siddacious/SA-45/images/fuuuuuuuuuck.png

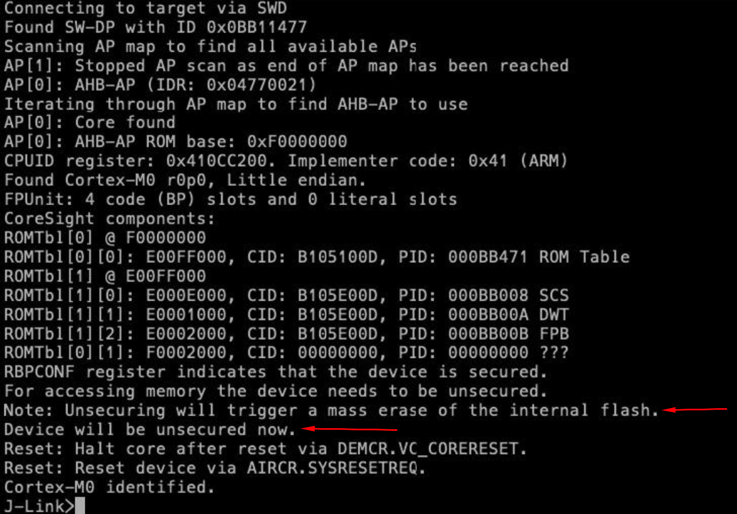
images/fuuuuuuuuuck.png
