siddacious/SA-45/images/guess_ill_stick_to_my_day_job.png

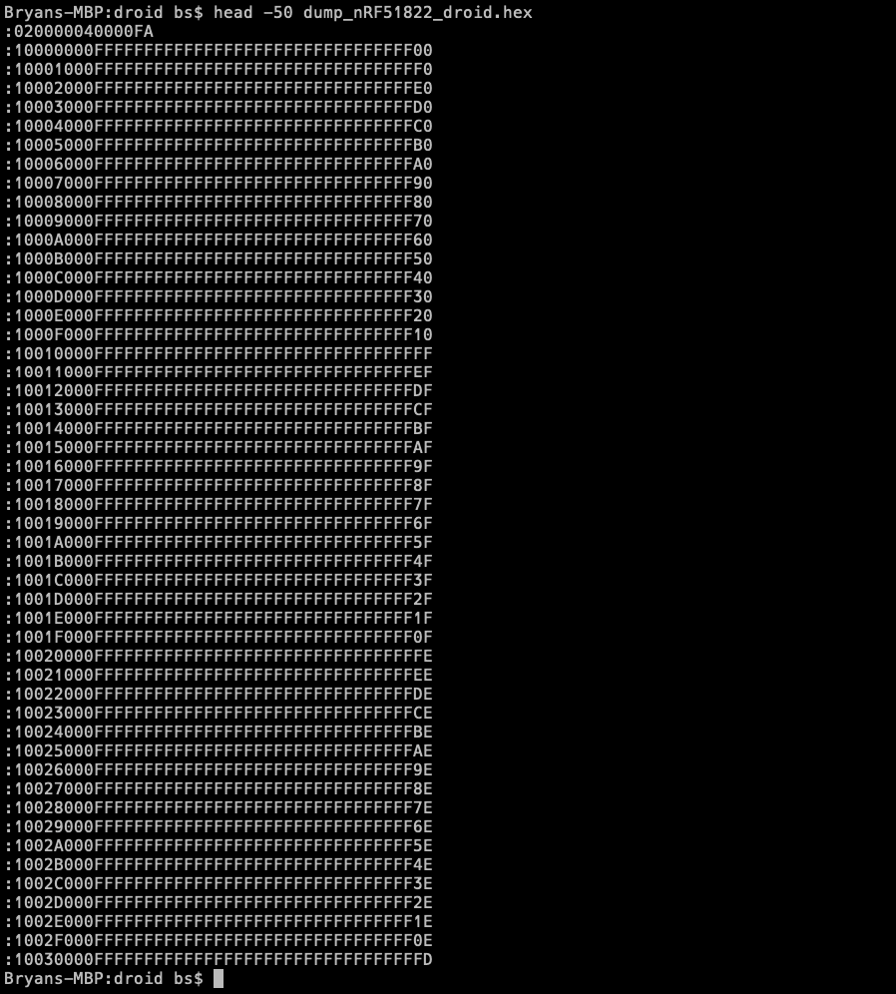
images/guess_ill_stick_to_my_day_job.png
