siddacious/SA-45/images/S20190909_001.jpg

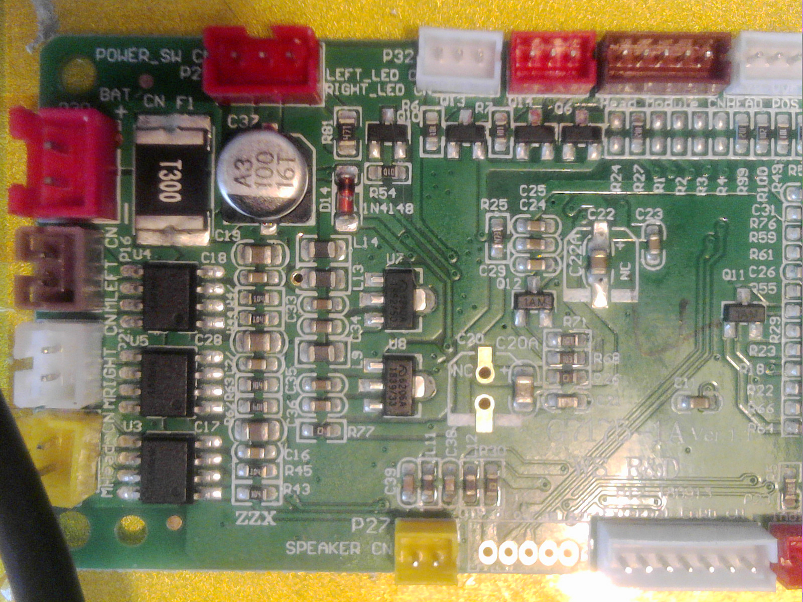
images/S20190909_001.jpg
