siddacious/SA-45/images/S20190909_002.jpg

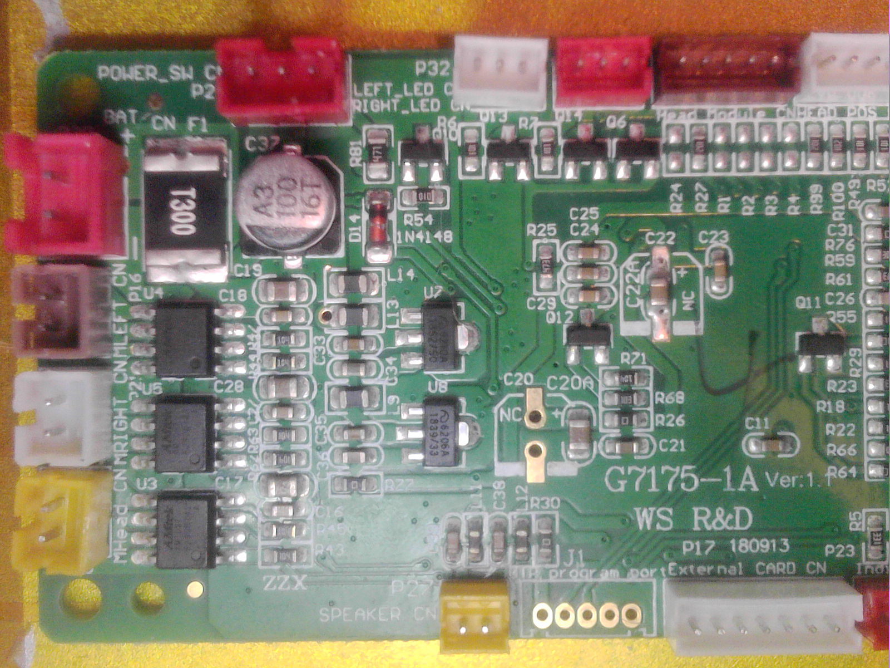
images/S20190909_002.jpg
