siddacious/SA-45/images/S20190909_003.jpg

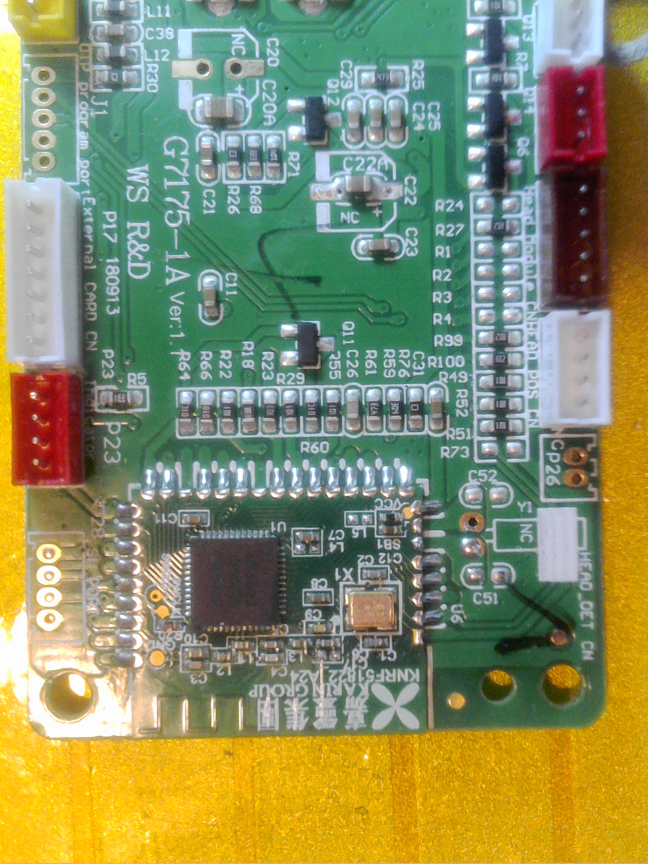
images/S20190909_003.jpg
