siddacious/SA-45/images/S20190909_006.jpg

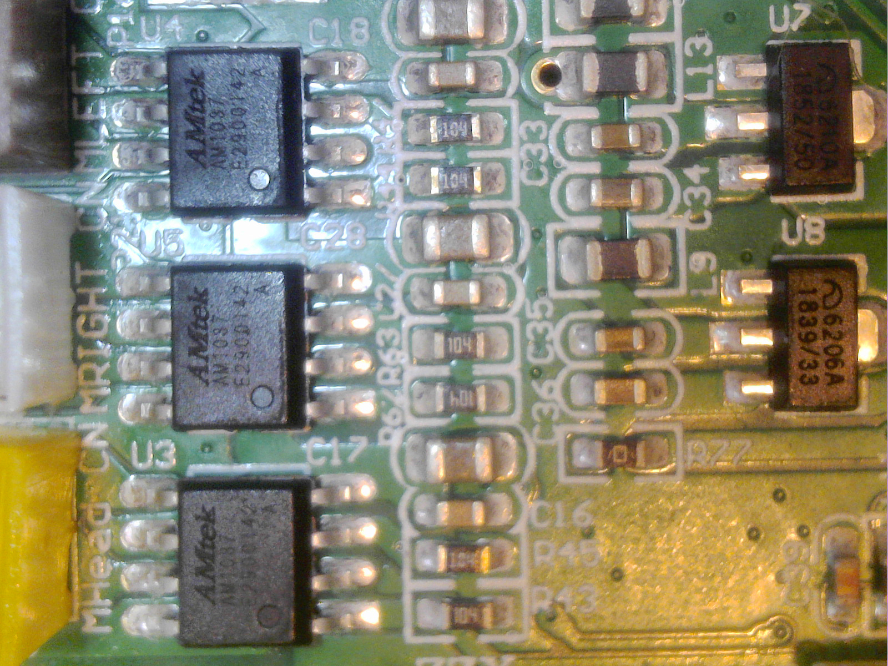
images/S20190909_006.jpg
