siddacious/SA-45/images/S20190909_007.jpg

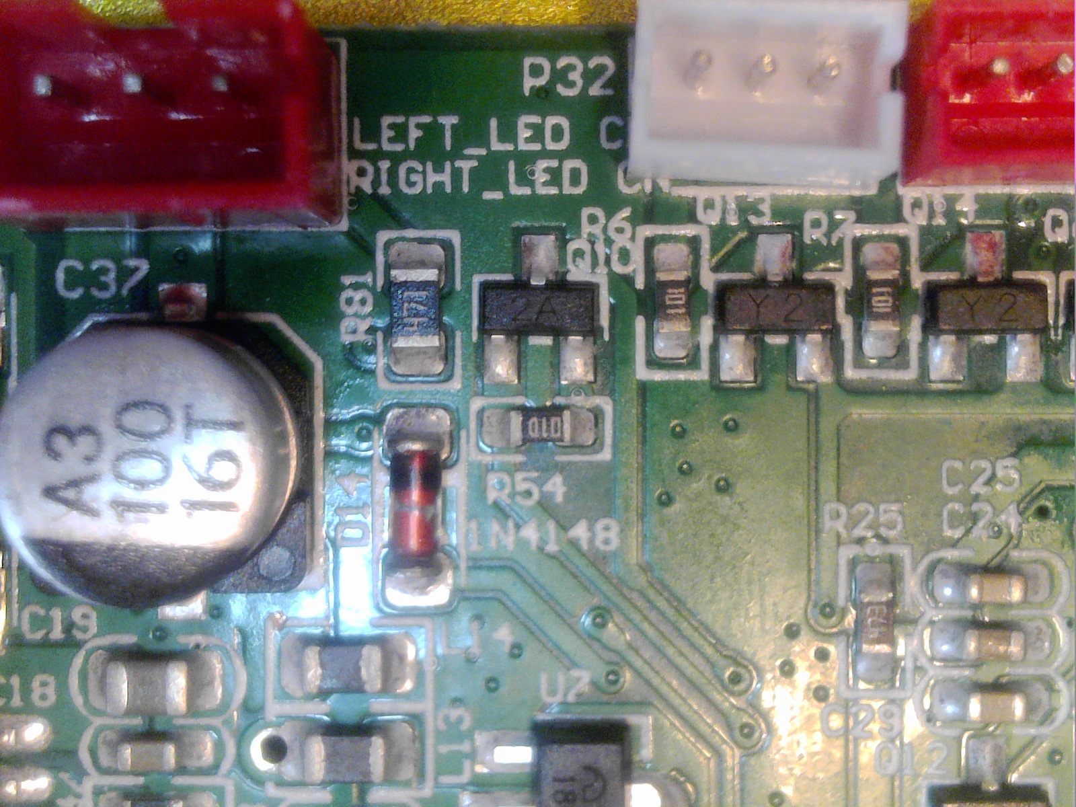
images/S20190909_007.jpg
