siddacious/SA-45/images/S20190909_009.jpg

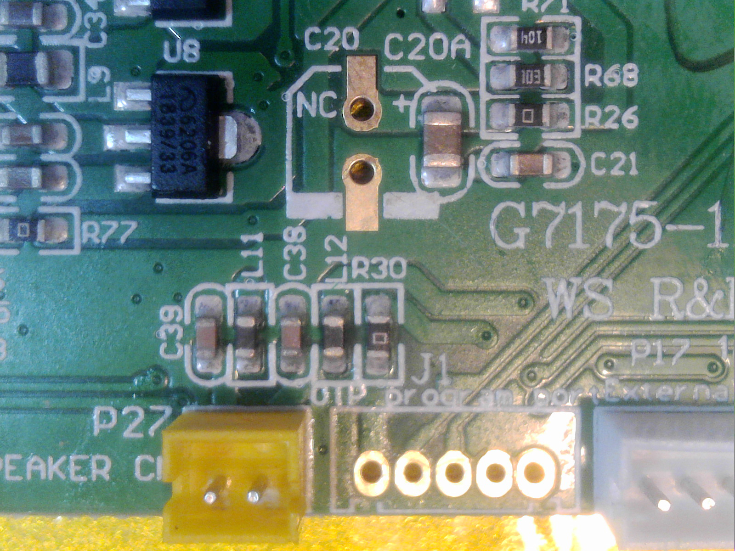
images/S20190909_009.jpg
