siddacious/SA-45/images/S20190909_010.jpg

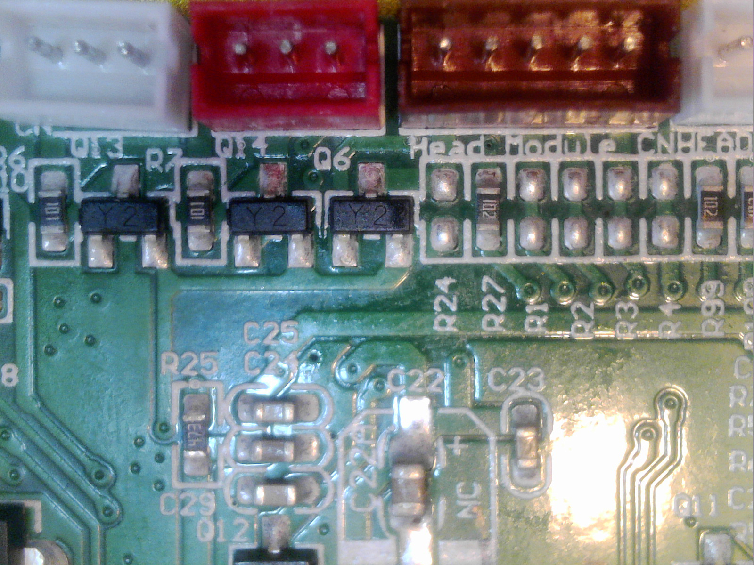
images/S20190909_010.jpg
