siddacious/SA-45/images/S20190909_011.jpg

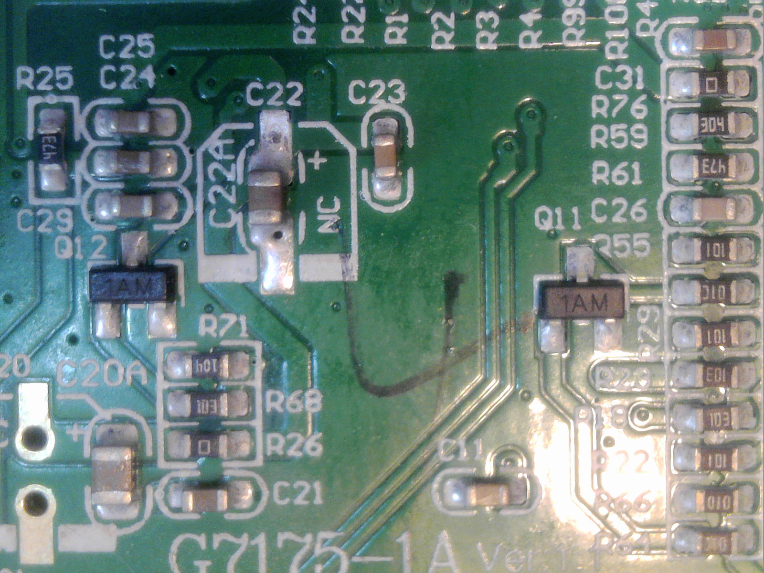
images/S20190909_011.jpg
