siddacious/SA-45/images/S20190909_012.jpg

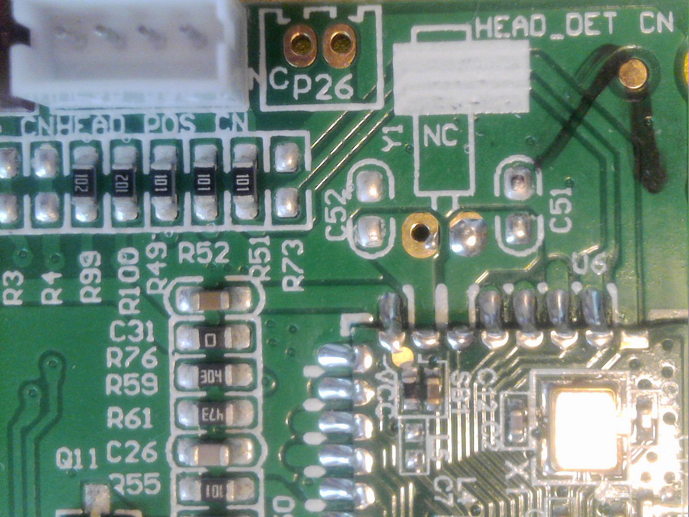
images/S20190909_012.jpg
