siddacious/SA-45/images/S20190909_014.jpg

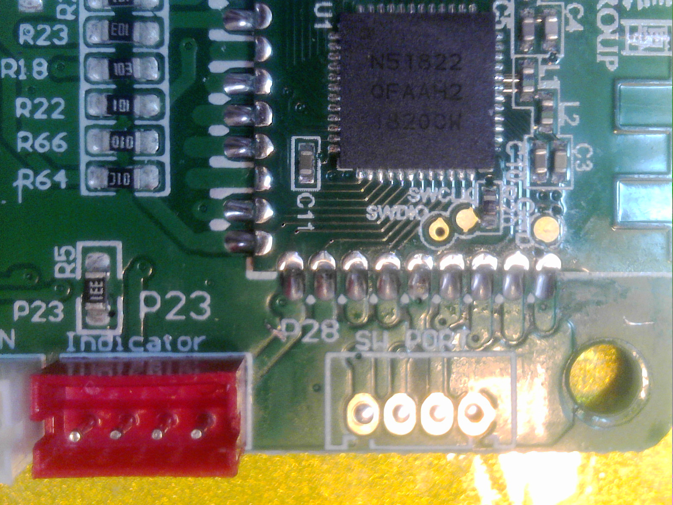
images/S20190909_014.jpg
