siddacious/SA-45/images/S20190909_015.jpg

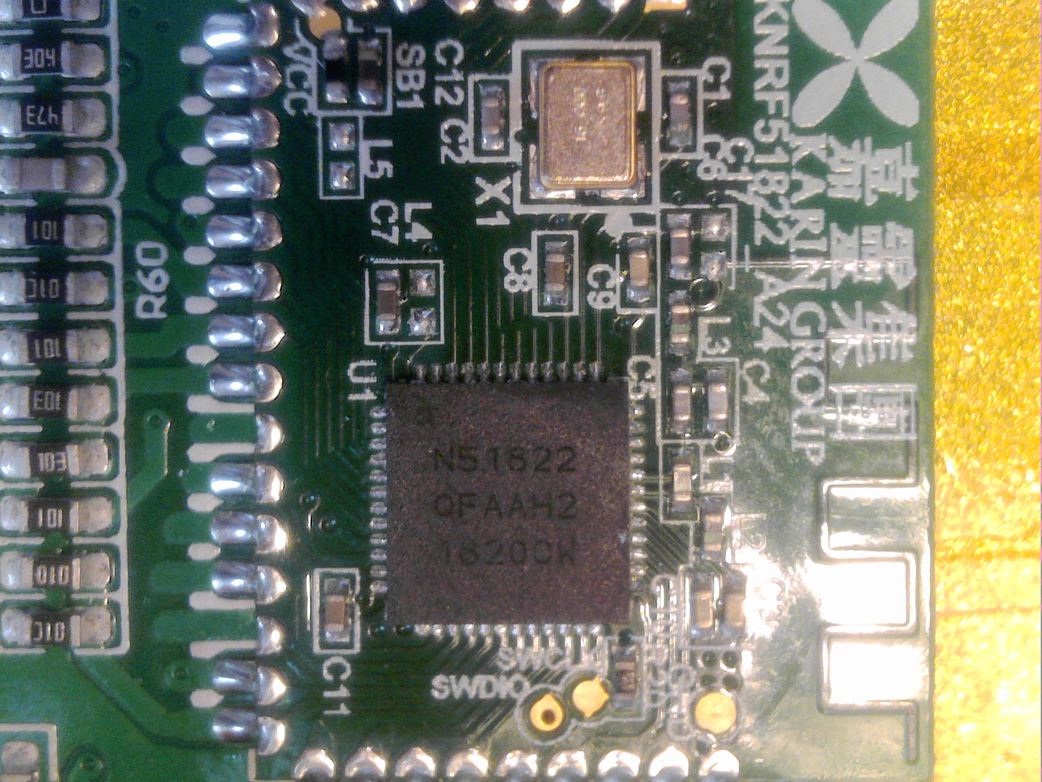
images/S20190909_015.jpg
