siddacious/SA-45/images/S20190909_016.jpg

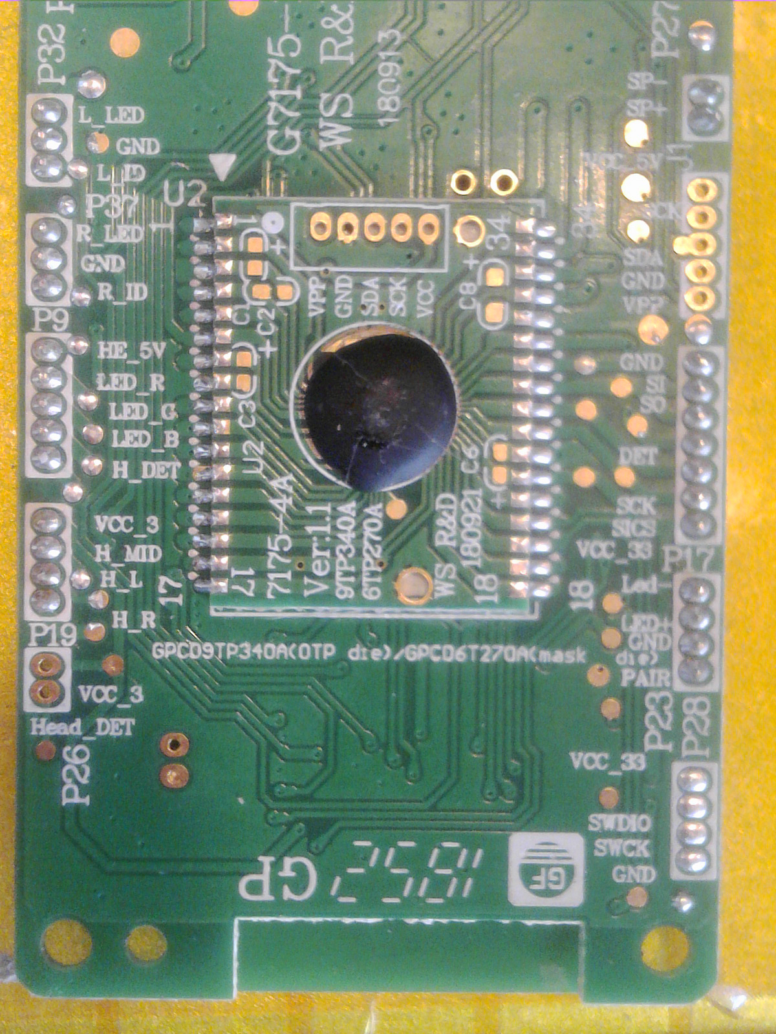
images/S20190909_016.jpg
