siddacious/SA-45/images/S20190909_017.jpg

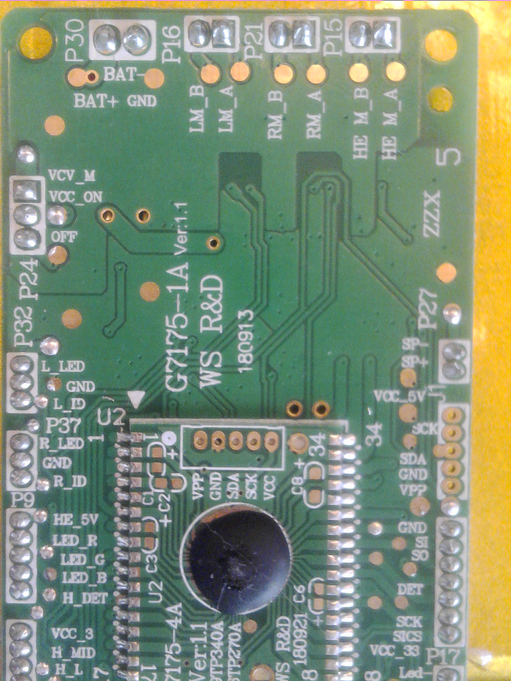
images/S20190909_017.jpg
