siddacious/SA-45/images/S20190909_018.jpg

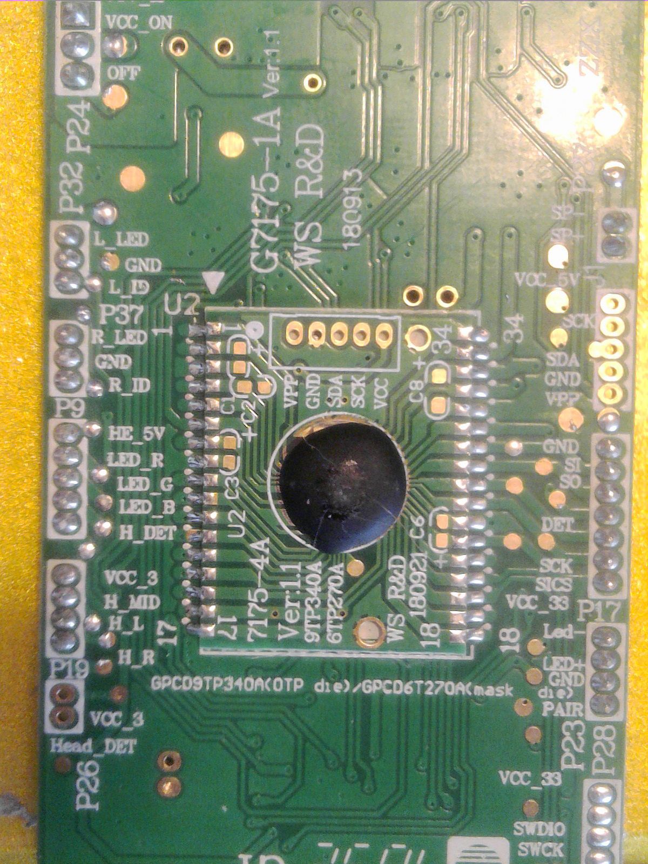
images/S20190909_018.jpg
