siddacious/SA-45/images/schem_V1_lowres.png

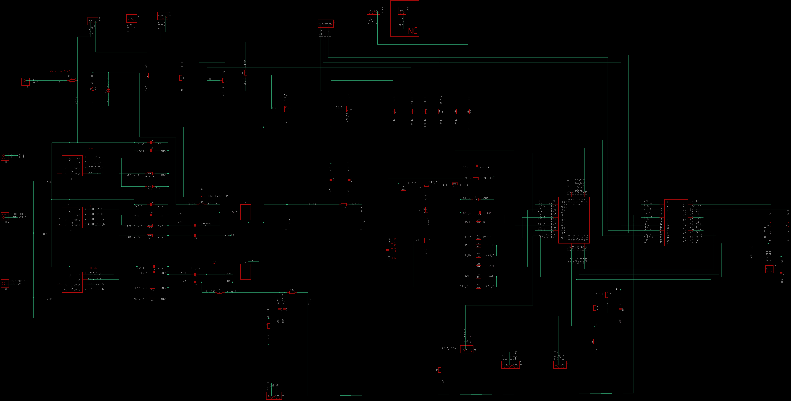
images/schem_V1_lowres.png
